mdh1418/LabMonitorUROP/LabMonitor/LabMonitor/Micropython/bme680-micropython-test/BME680-wipy.JPG

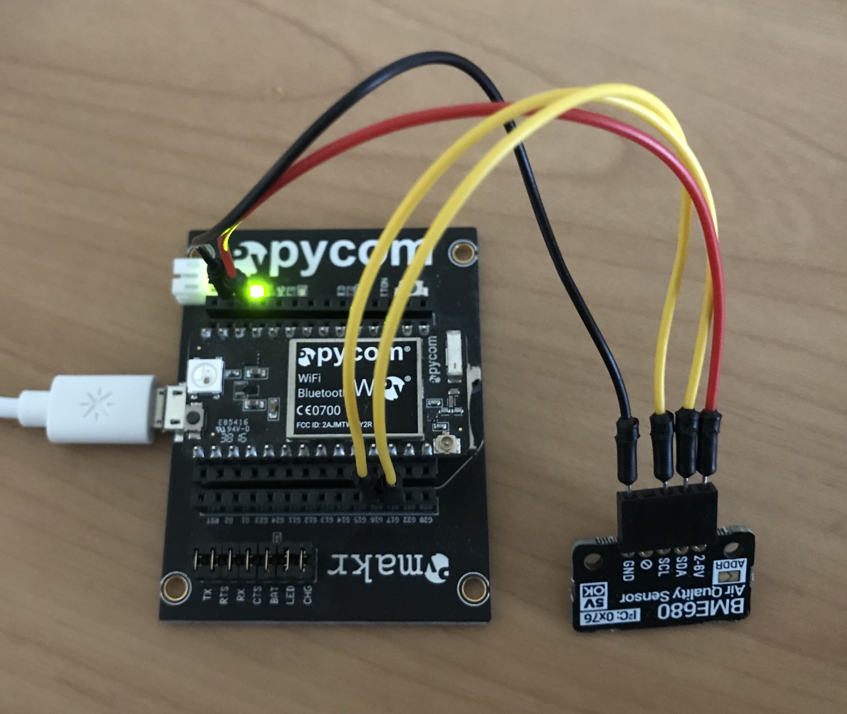
LabMonitor/LabMonitor/Micropython/bme680-micropython-test/BME680-wipy.JPG
