mdh1418/LabMonitorUROP/LabMonitor/LabMonitor/Micropython/bme680-micropython-test/adds-leak-sensor/BME-680+leak.JPG

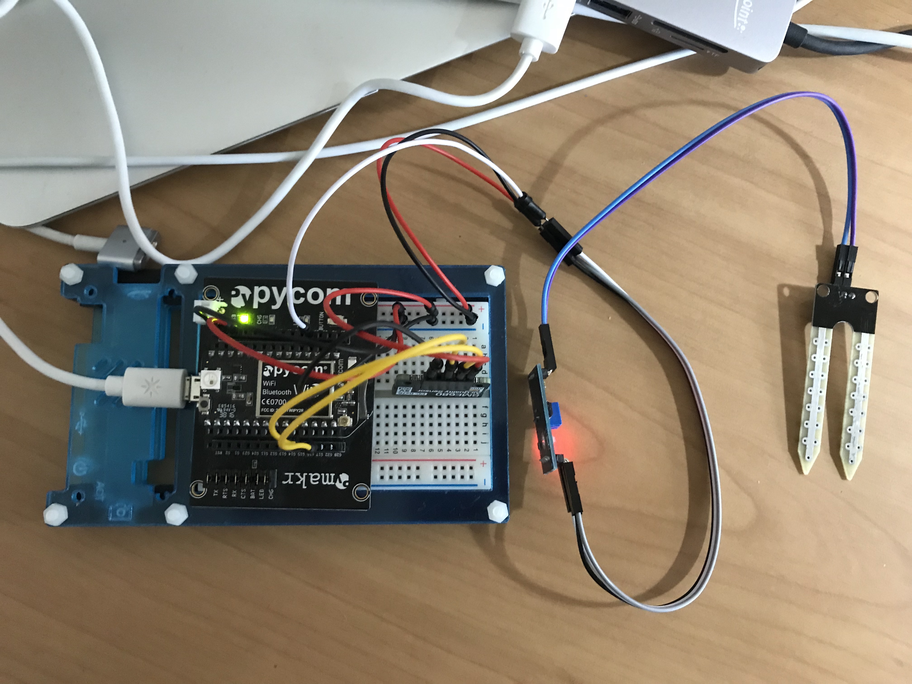
LabMonitor/LabMonitor/Micropython/bme680-micropython-test/adds-leak-sensor/BME-680+leak.JPG
