mdh1418/LabMonitorUROP/LabMonitor/Images/ESP_Barebones.png

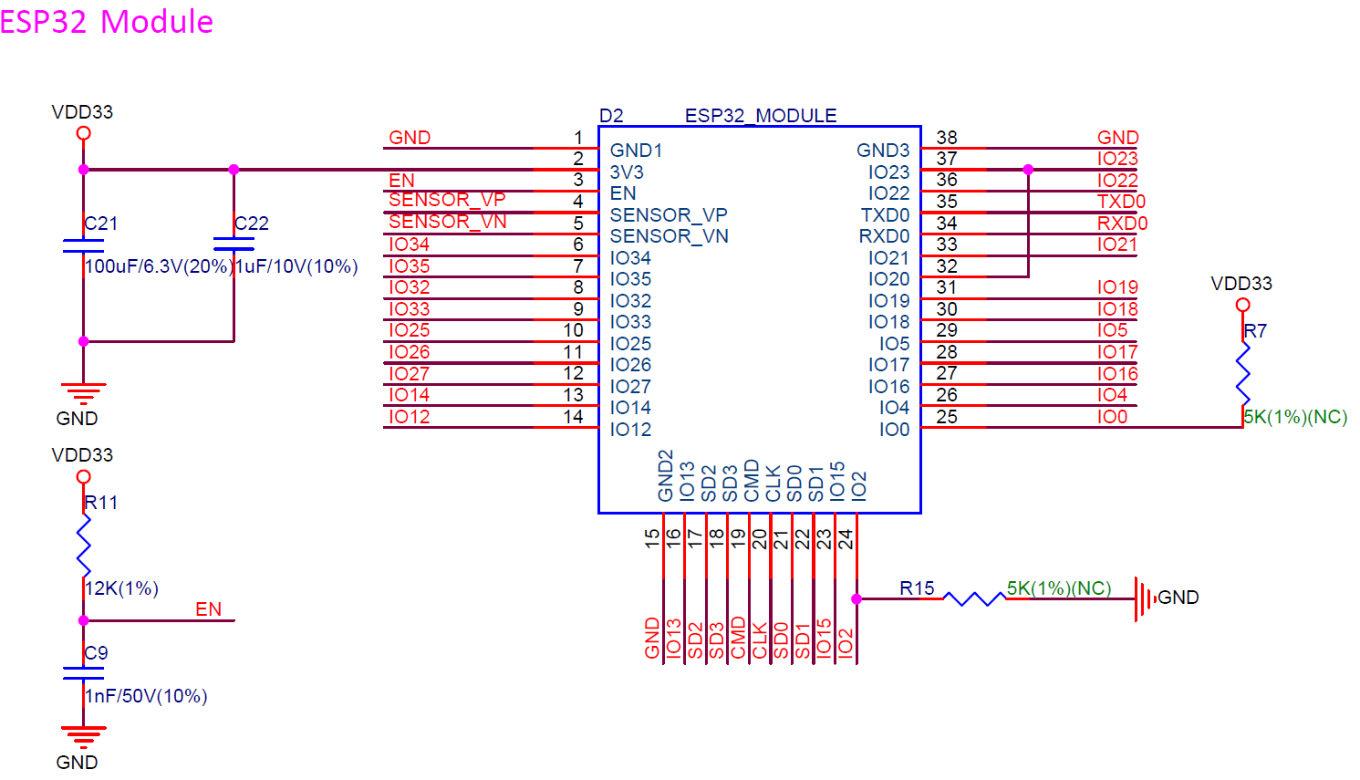
LabMonitor/Images/ESP_Barebones.png
