mdh1418/LabMonitorUROP/LabMonitor/LabMonitor/Kicad/LabMonitor-kicad-lib/template/1593K_Enclosure/meta/1593K3B.jpg

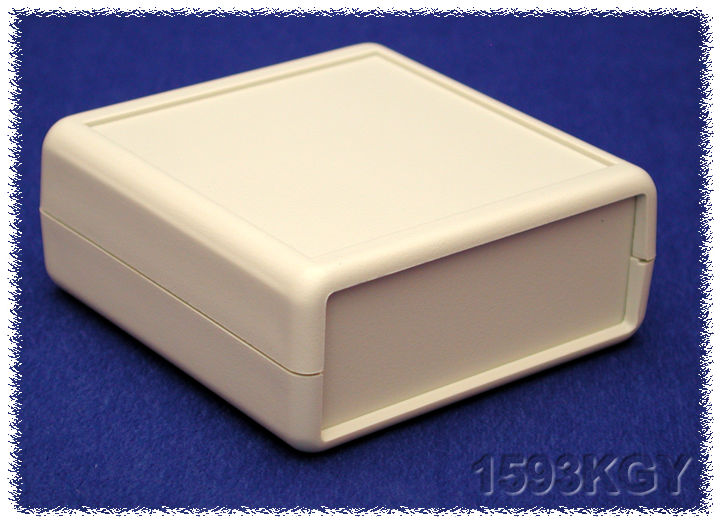
LabMonitor/LabMonitor/Kicad/LabMonitor-kicad-lib/template/1593K_Enclosure/meta/1593K3B.jpg
