mdh1418/LabMonitorUROP/LabMonitor/LabMonitor/Kicad/LabMonitor-kicad-lib/template/1593K_Enclosure/meta/brd.png

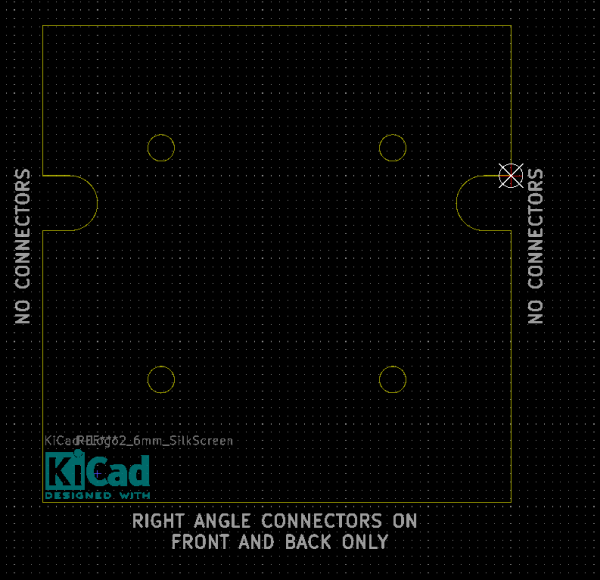
LabMonitor/LabMonitor/Kicad/LabMonitor-kicad-lib/template/1593K_Enclosure/meta/brd.png
