mdh1418/LabMonitorUROP/LabMonitor/LabMonitor/Kicad/LabMonitor-kicad-lib/template/Arduino_As_Uno_R3/meta/brd.png

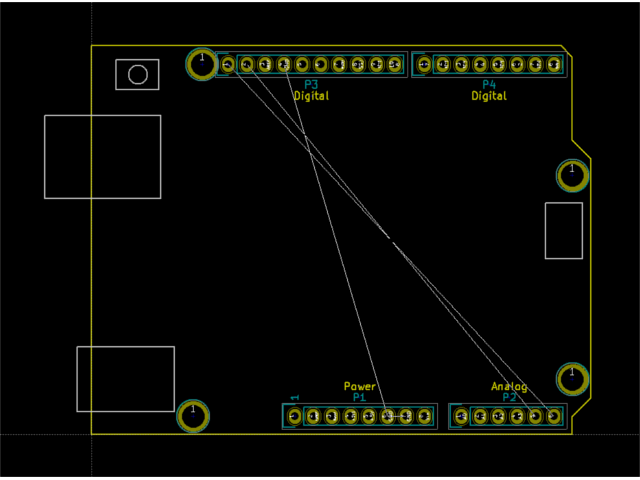
LabMonitor/LabMonitor/Kicad/LabMonitor-kicad-lib/template/Arduino_As_Uno_R3/meta/brd.png
