mdh1418/LabMonitorUROP/LabMonitor/LabMonitor/Kicad/LabMonitor-kicad-lib/template/Arduino_Mega_R3/meta/brd.png

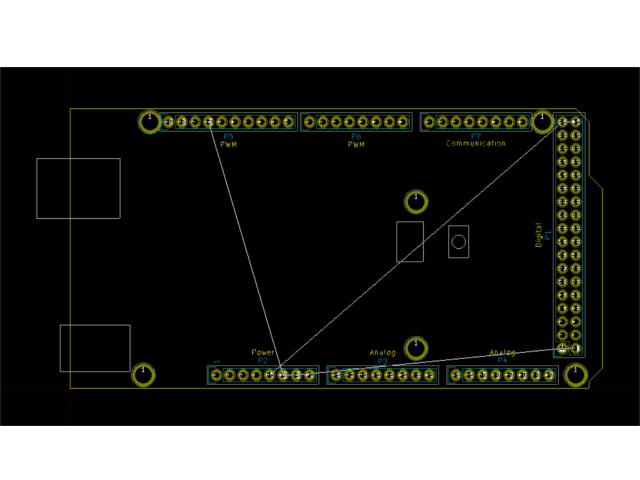
LabMonitor/LabMonitor/Kicad/LabMonitor-kicad-lib/template/Arduino_Mega_R3/meta/brd.png
