mdh1418/LabMonitorUROP/LabMonitor/LabMonitor/Kicad/LabMonitor-kicad-lib/template/Arduino_Micro/meta/brd.png

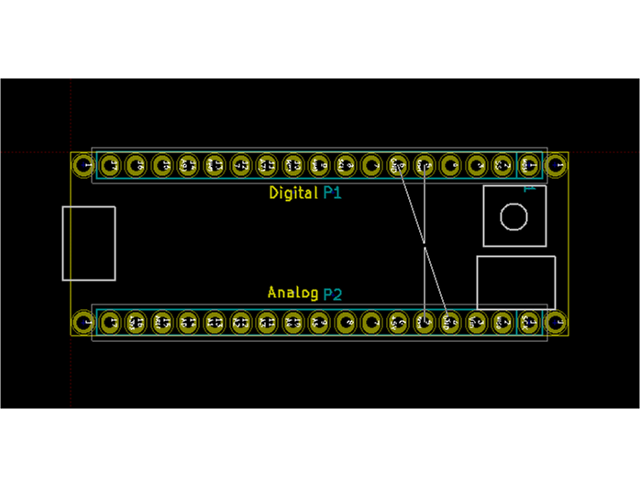
LabMonitor/LabMonitor/Kicad/LabMonitor-kicad-lib/template/Arduino_Micro/meta/brd.png
