mdh1418/LabMonitorUROP/LabMonitor/LabMonitor/Kicad/LabMonitor-kicad-lib/template/stm32f100-discovery-shield/meta/board_stm32vl_discovery.png

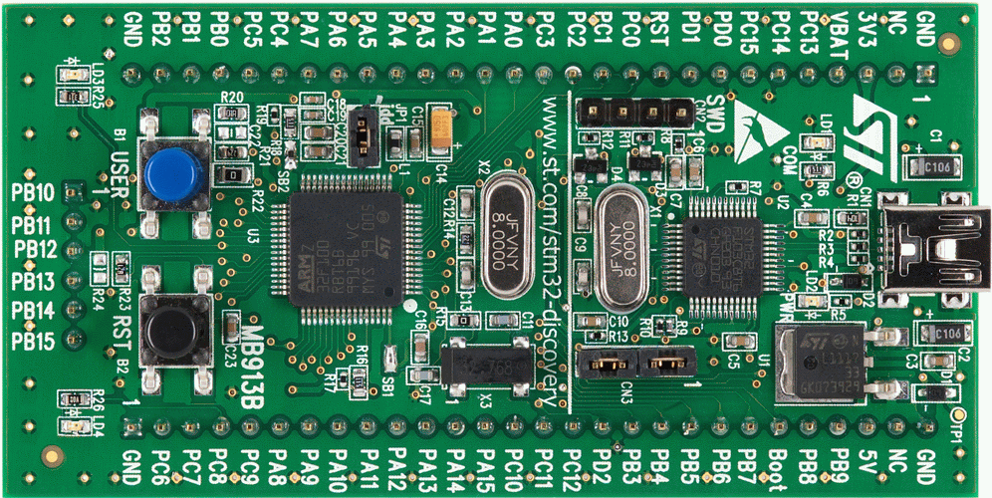
LabMonitor/LabMonitor/Kicad/LabMonitor-kicad-lib/template/stm32f100-discovery-shield/meta/board_stm32vl_discovery.png
