mdh1418/LabMonitorUROP/LabMonitor/LabMonitor/Kicad/LabMonitor-kicad-lib/template/ti-stellaris-boosterpack40/meta/launchpad_standard40.png

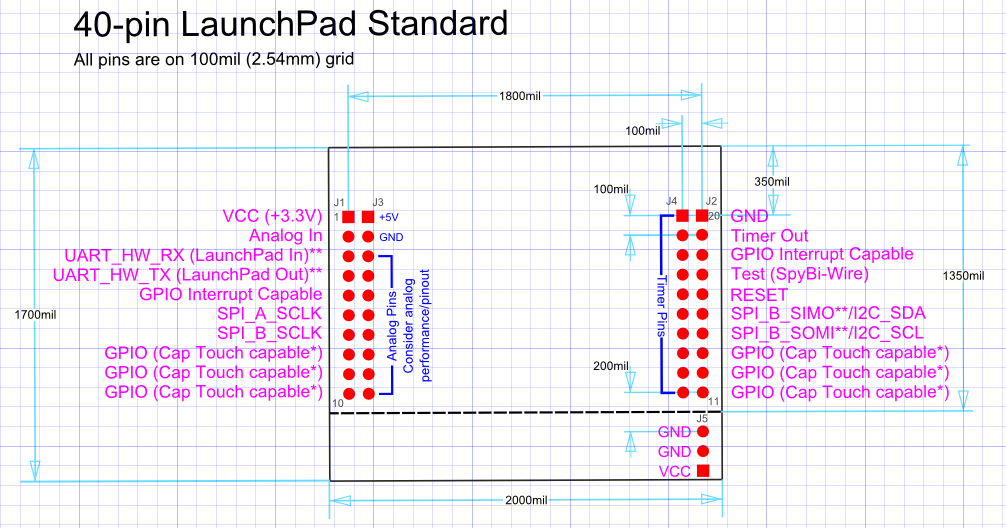
LabMonitor/LabMonitor/Kicad/LabMonitor-kicad-lib/template/ti-stellaris-boosterpack40/meta/launchpad_standard40.png
